rmn388/dog-treat-dispenser/cad/Assembly 1 - Dispenser and Servo.JPG

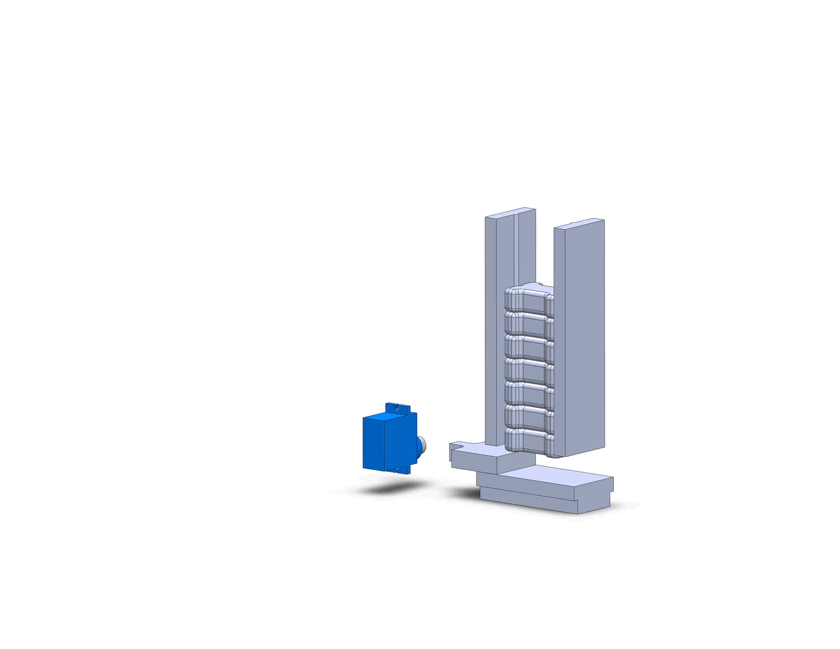
cad/Assembly 1 - Dispenser and Servo.JPG
